saganash-21/Analog-to-Digital-Acoustic-Signal-Pipeline/schematics/Analog signal processing sch.sch

## EAGLE design schematics/Analog signal processing sch.sch (2026-07-01)

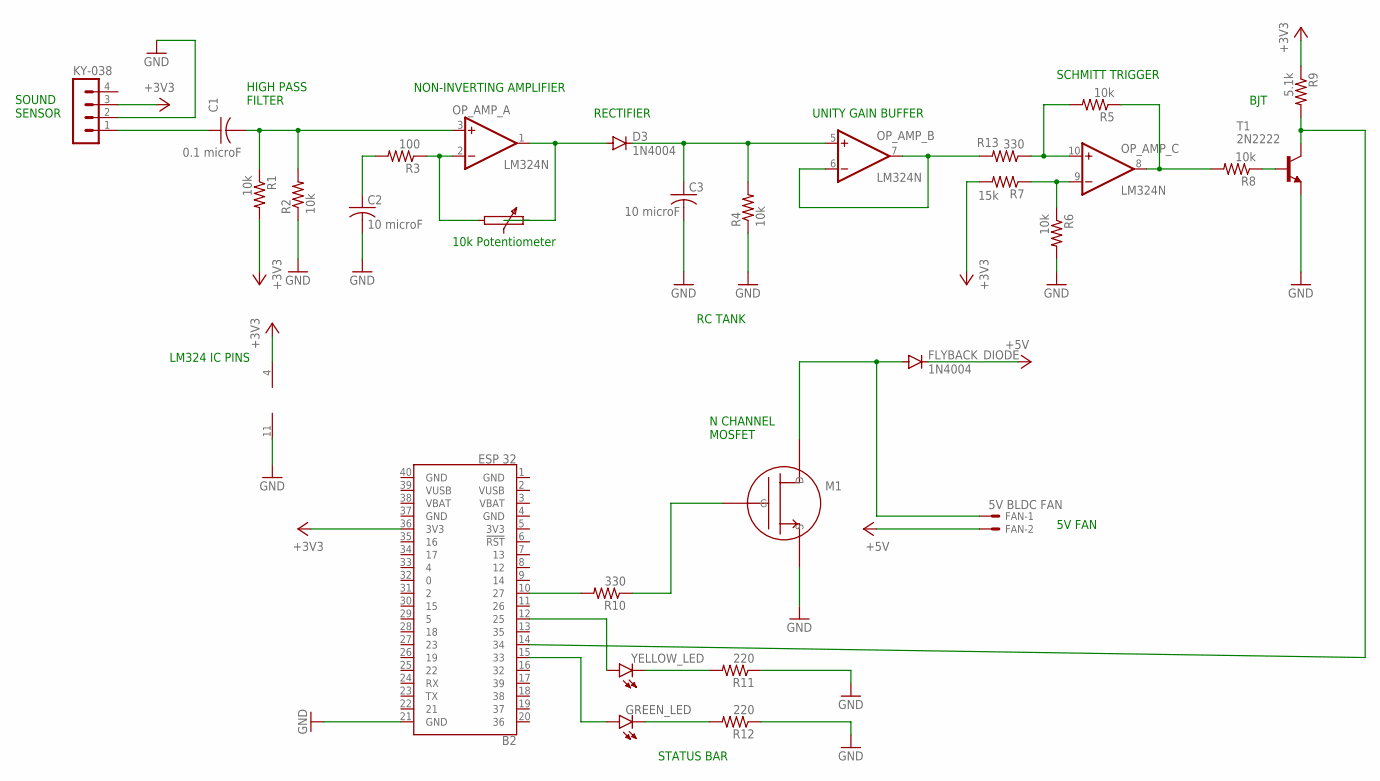
[picture p7: schematic Analog signal processing sch.sch]

Parts:
B2: ESP 32; ESP32_THING_NO_ANT
C1: 0.1 microF; C025-024X044
C2, C3: 10 microF; C025-024X044
D3: 1N4004; DO41-10
FAN: 5V BLDC FAN; 22-23-2021
FLYBACK_DIODE: 1N4004; DO41-10
GREEN_LED: HLMP6
KY-038: MA04-1
OP_AMP_: LM324N; DIL14
R1, R2, R4, R5, R6, R8: 10k; 0204/7
R3: 100; 0204/7
R7: 15k; 0204/7
R9: 5.1k; 0204/7
R10, R13: 330; 0204/7
R11, R12: 220; 0204/7
T1: 2N2222; TO18
YELLOW_LED: HLMP6

Connections:
+3V3: B2.36 (3V3), KY-038.3, OP_AMP_.4 (V+), R1.2, R7.2, R9.1
+5V: FAN.2, FLYBACK_DIODE.C
GND: B2.21 (GND), C2.2, C3.2, KY-038.2, OP_AMP_.11 (V-), R2.1, R4.1, R6.2, R11.1, R12.1, T1.1 (E)
unnamed: C1.1, KY-038.1
unnamed: C1.2, OP_AMP_.3 (+IN), R1.1, R2.2
unnamed: OP_AMP_.2 (-IN), R3.1
unnamed: D3.A, OP_AMP_.1 (OUT)
unnamed: C2.1, R3.2
unnamed: C3.1, D3.C, OP_AMP_.5 (+IN), R4.2
unnamed: OP_AMP_.6 (-IN), OP_AMP_.7 (OUT), R13.2
unnamed: OP_AMP_.8 (OUT), R5.1, R8.2
unnamed: R8.1, T1.2 (B)
unnamed: OP_AMP_.9 (-IN), R6.1, R7.1
unnamed: B2.14 (34), R9.2, T1.3 (C)
unnamed: B2.10 (27), R10.2
unnamed: OP_AMP_.10 (+IN), R5.2, R13.1
unnamed: FAN.1, FLYBACK_DIODE.A
unnamed: B2.15 (33), GREEN_LED.A
unnamed: B2.12 (25), YELLOW_LED.A
unnamed: GREEN_LED.K, R12.2
unnamed: R11.2, YELLOW_LED.K

Notes on the sheet:
NON-INVERTING AMPLIFIER
RC TANK
SOUND SENSOR
UNITY GAIN BUFFER
SCHMITT TRIGGER
HIGH PASS FILTER
STATUS BAR
5V FAN
10k Potentiometer
BJT
N CHANNEL MOSFET
RECTIFIER
LM324 IC PINS
